mbalestrini/mpw6_caravel_hacks_soc_bringup/devlog/mpw6_048-Caravel_serial_test.png

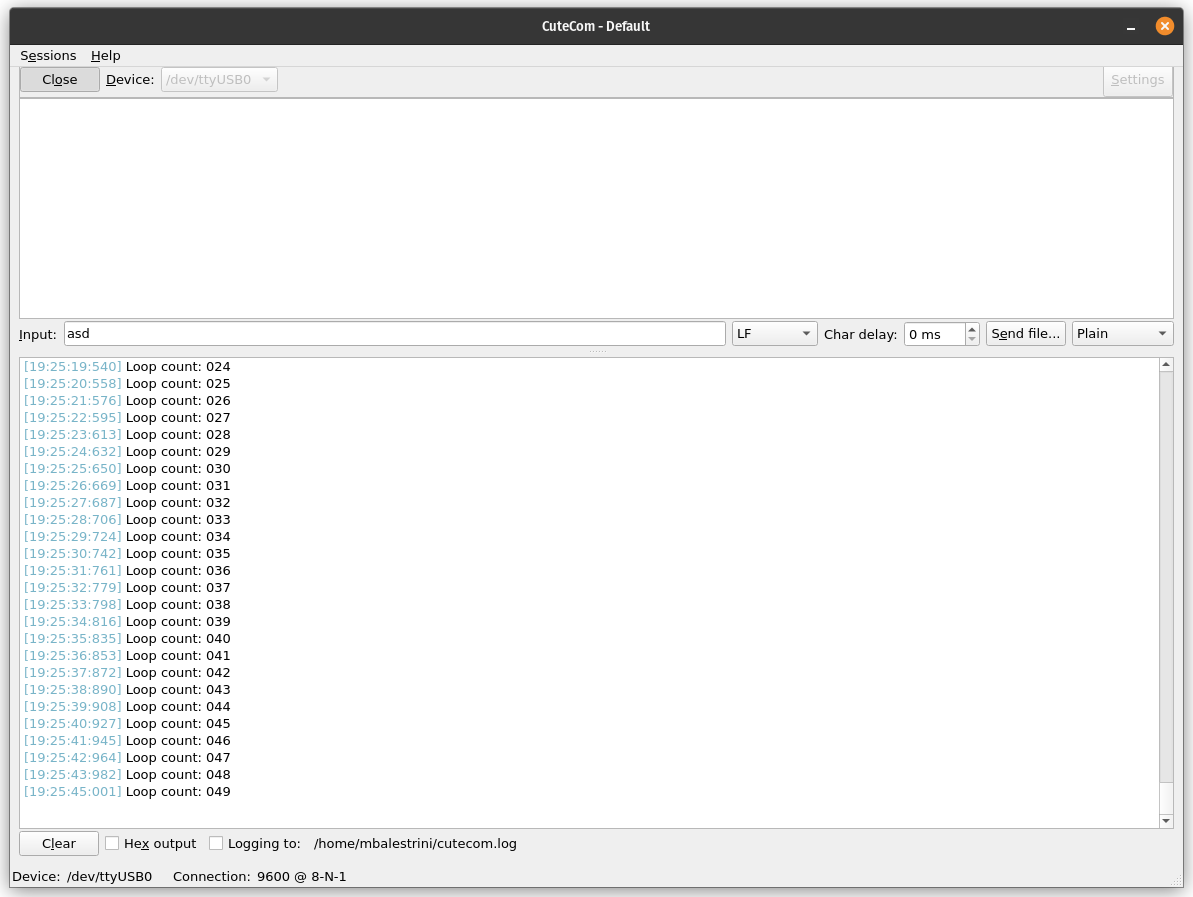
devlog/mpw6_048-Caravel_serial_test.png
