mbalestrini/mpw6_caravel_hacks_soc_bringup/devlog/mpw6_048-first_test-Clock_X1.png

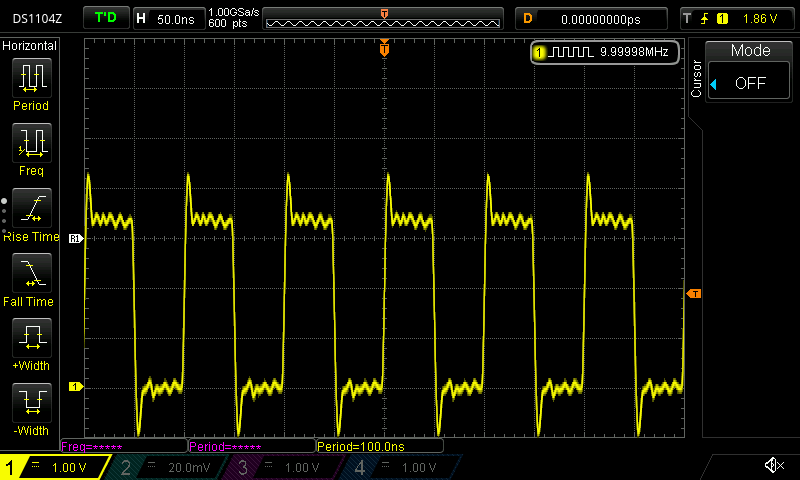
devlog/mpw6_048-first_test-Clock_X1.png
