mbalestrini/mpw6_caravel_hacks_soc_bringup/devlog/mpw6_048-first_test-Init_Sequence-Screenshot from 2023-12-30 17-56-38.png

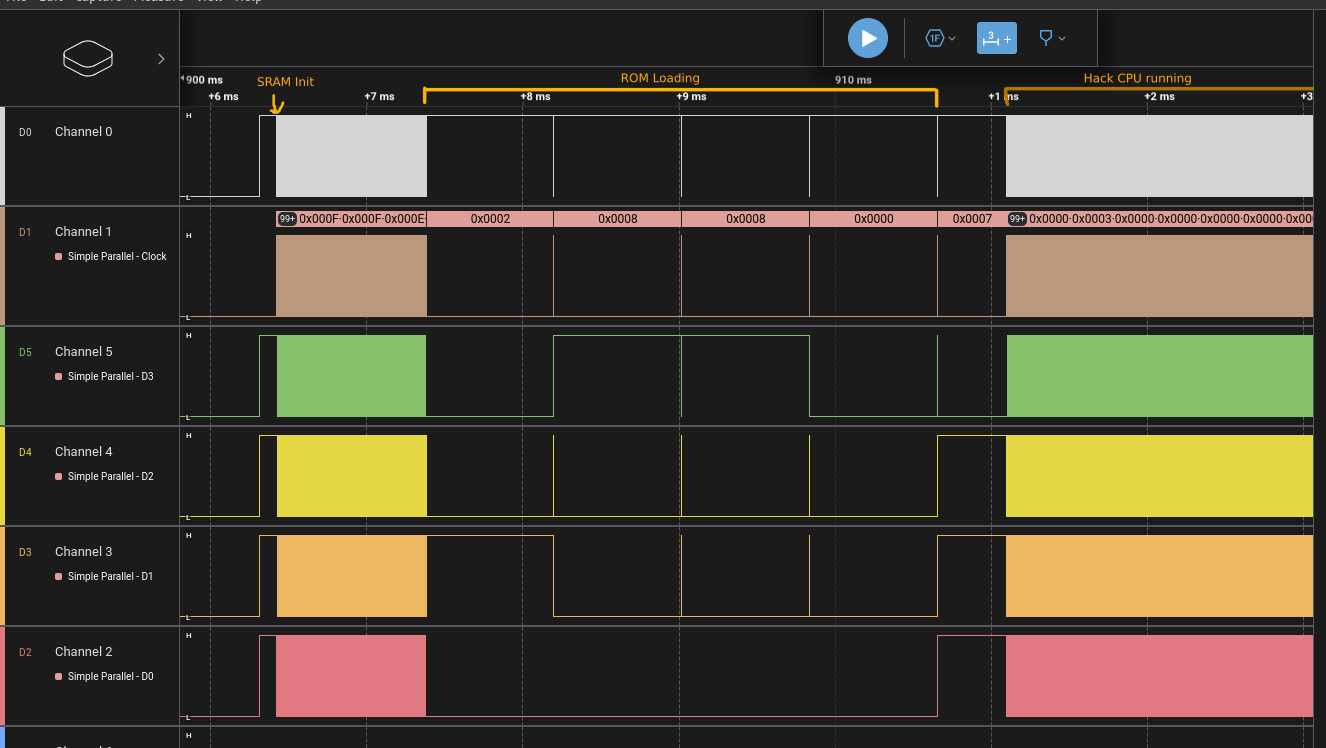
devlog/mpw6_048-first_test-Init_Sequence-Screenshot from 2023-12-30 17-56-38.png
