mbalestrini/mpw6_caravel_hacks_soc_bringup/devlog/mpw6_048-first_test-IO28-20231228-B.png

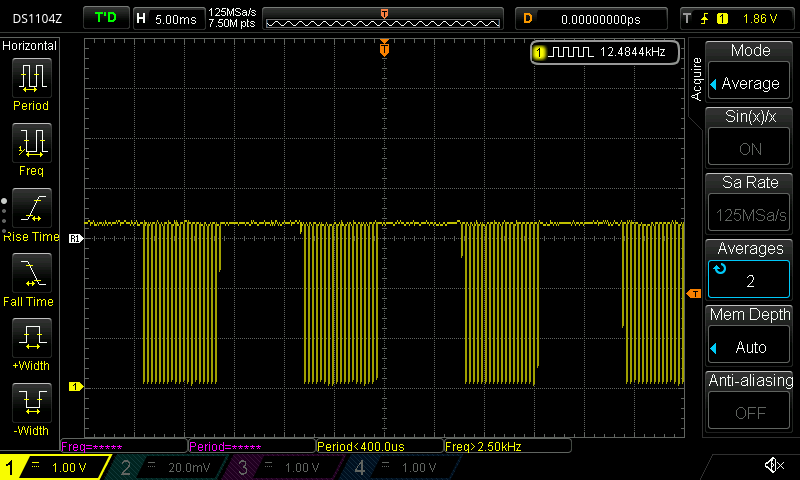
devlog/mpw6_048-first_test-IO28-20231228-B.png
