mbalestrini/mpw6_caravel_hacks_soc_bringup/devlog/mpw6_048-first_test-ROM_Init-Screenshot from 2023-12-30 17-48-50.png

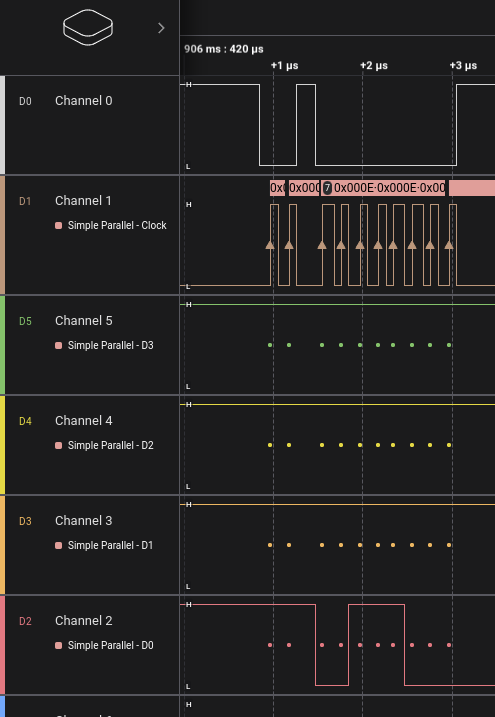
devlog/mpw6_048-first_test-ROM_Init-Screenshot from 2023-12-30 17-48-50.png
