mbalestrini/mpw6_caravel_hacks_soc_bringup/devlog/mpw6_048-test_mem_1-RAM_IO_3_pulldown_10k-RAM_CS_CLK_SIO3-20240123.png

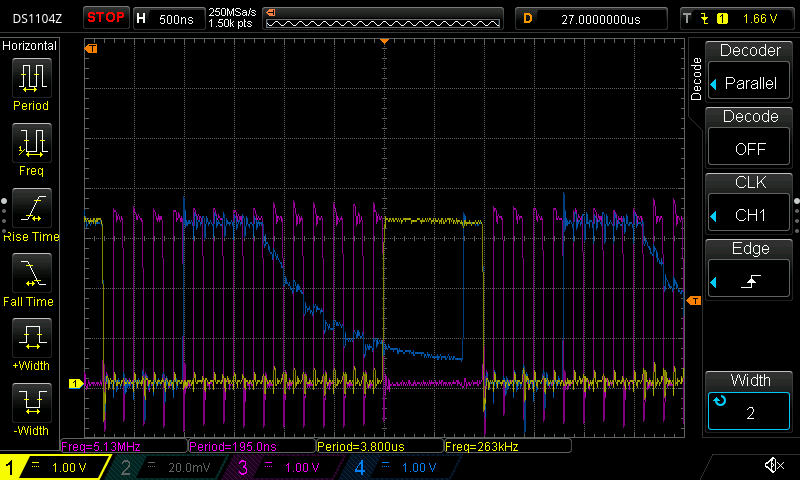
devlog/mpw6_048-test_mem_1-RAM_IO_3_pulldown_10k-RAM_CS_CLK_SIO3-20240123.png
