mbalestrini/mpw6_caravel_hacks_soc_bringup/devlog/_MG_6943.jpg

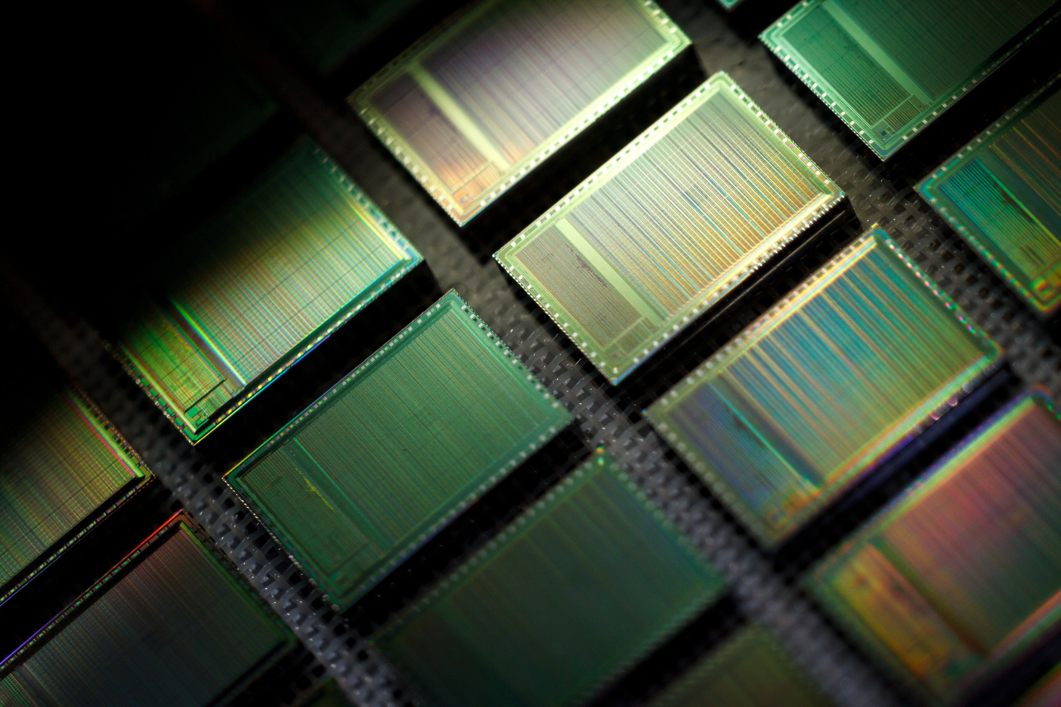
devlog/_MG_6943.jpg
