mbalestrini/mpw6_caravel_hacks_soc_bringup/devlog/_MG_6948.jpg

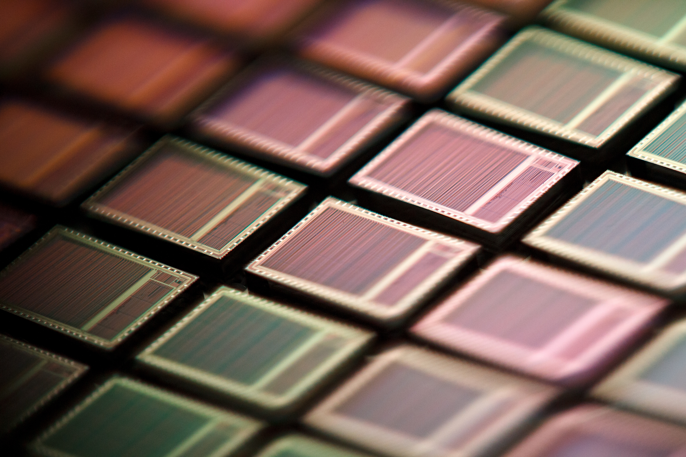
devlog/_MG_6948.jpg
