mbalestrini/mpw6_caravel_hacks_soc_bringup/devlog/DSC09348.jpg

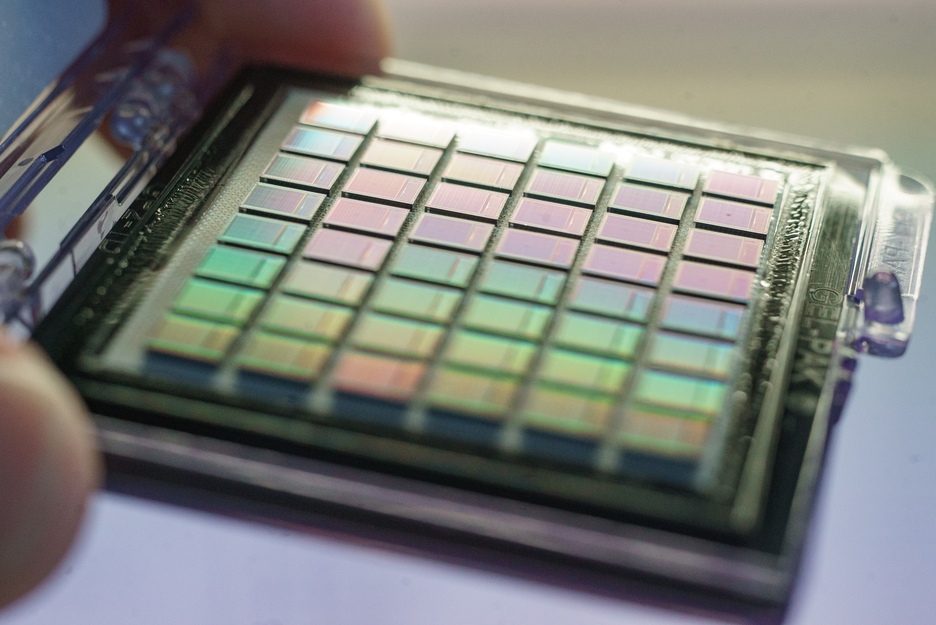
devlog/DSC09348.jpg
