mbalestrini/mpw6_caravel_hacks_soc_bringup/devlog/DSC09561.jpg

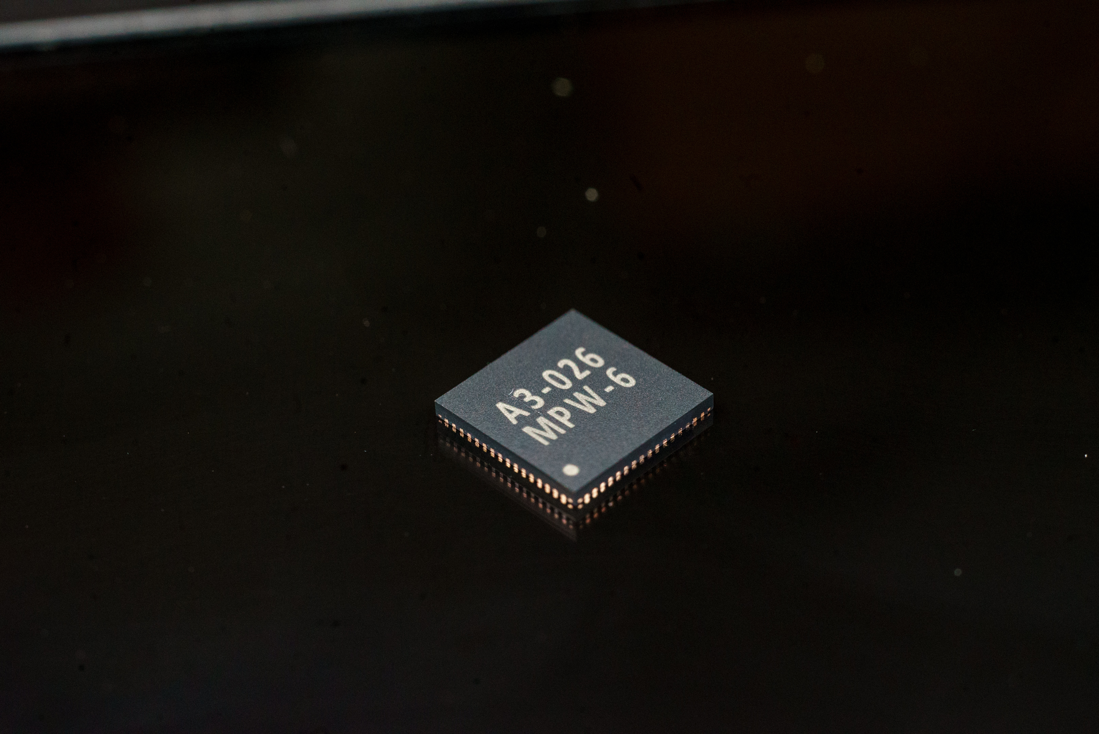
devlog/DSC09561.jpg
