mbalestrini/mpw6_caravel_hacks_soc_bringup/devlog/PXL_20231228_205425441.jpg

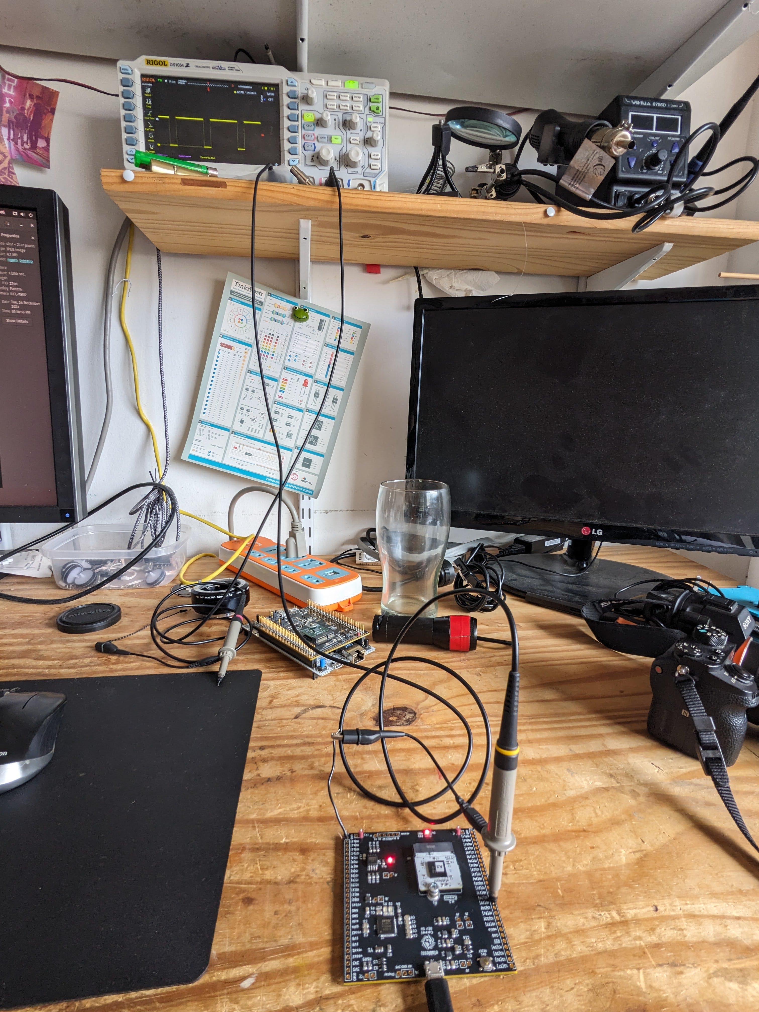
devlog/PXL_20231228_205425441.jpg
