mbalestrini/mpw6_caravel_hacks_soc_bringup/devlog/PXL_20231229_003644289.jpg

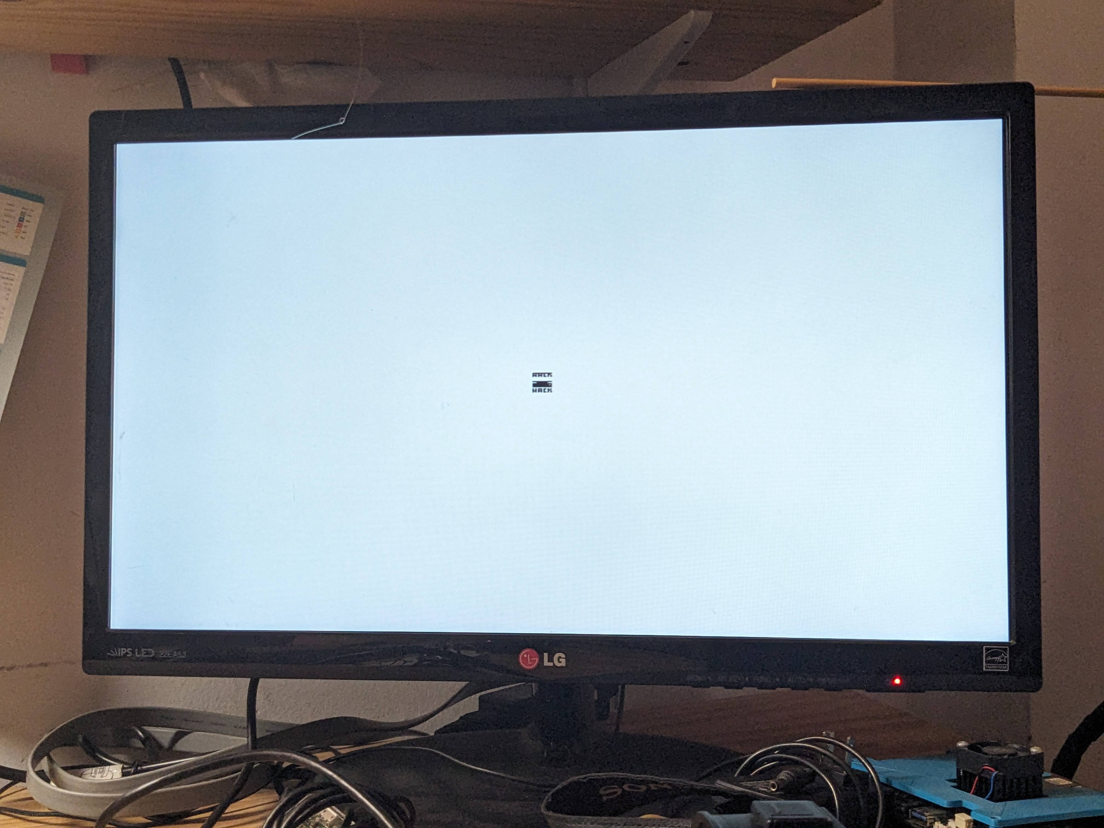
devlog/PXL_20231229_003644289.jpg
