mbalestrini/mpw6_caravel_hacks_soc_bringup/devlog/PXL_20231229_003654547.jpg

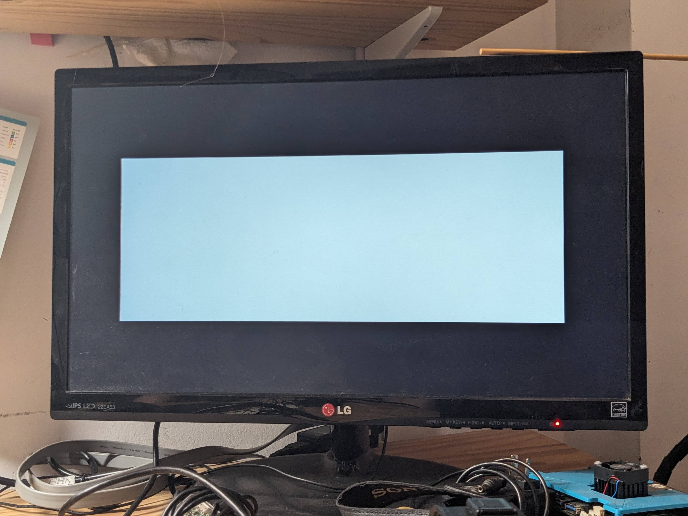
devlog/PXL_20231229_003654547.jpg
