mbalestrini/mpw6_caravel_hacks_soc_bringup/devlog/PXL_20231229_004134263.jpg

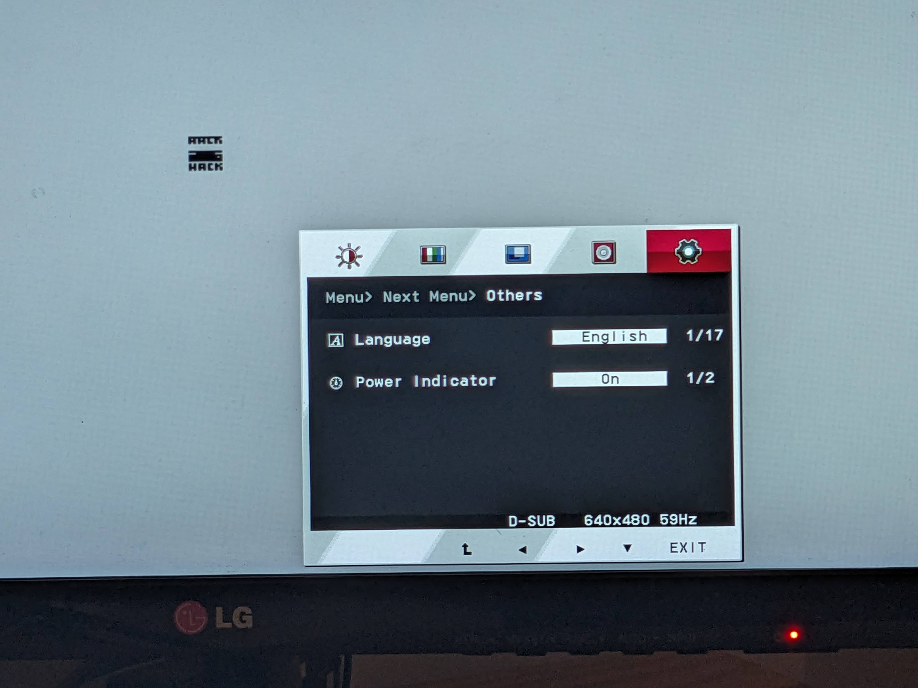
devlog/PXL_20231229_004134263.jpg
