mbalestrini/mpw6_caravel_hacks_soc_bringup/devlog/PXL_20231230_204112461.jpg

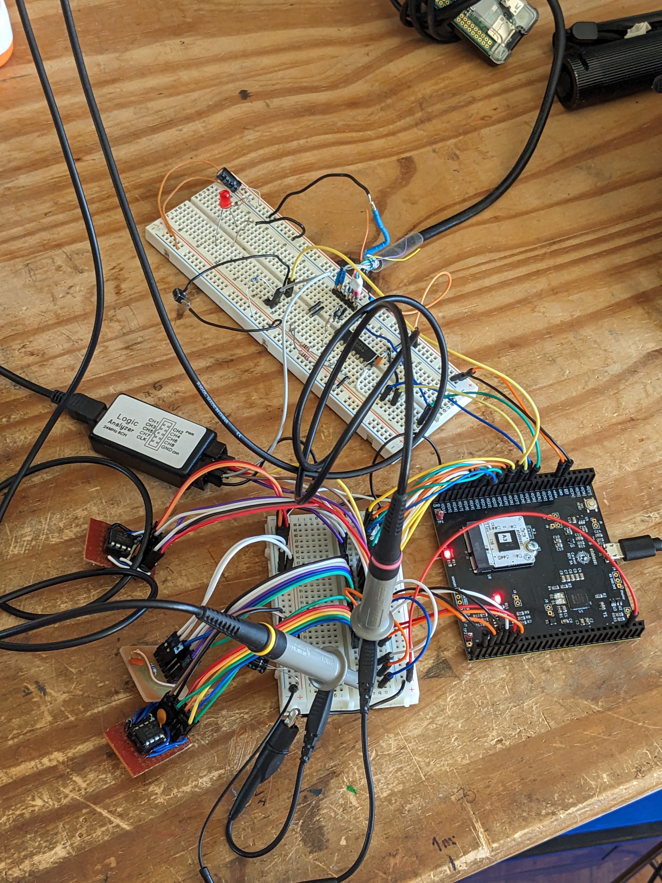
devlog/PXL_20231230_204112461.jpg
