mbalestrini/mpw6_caravel_hacks_soc_bringup/devlog/PXL_20231230_231902643.jpg

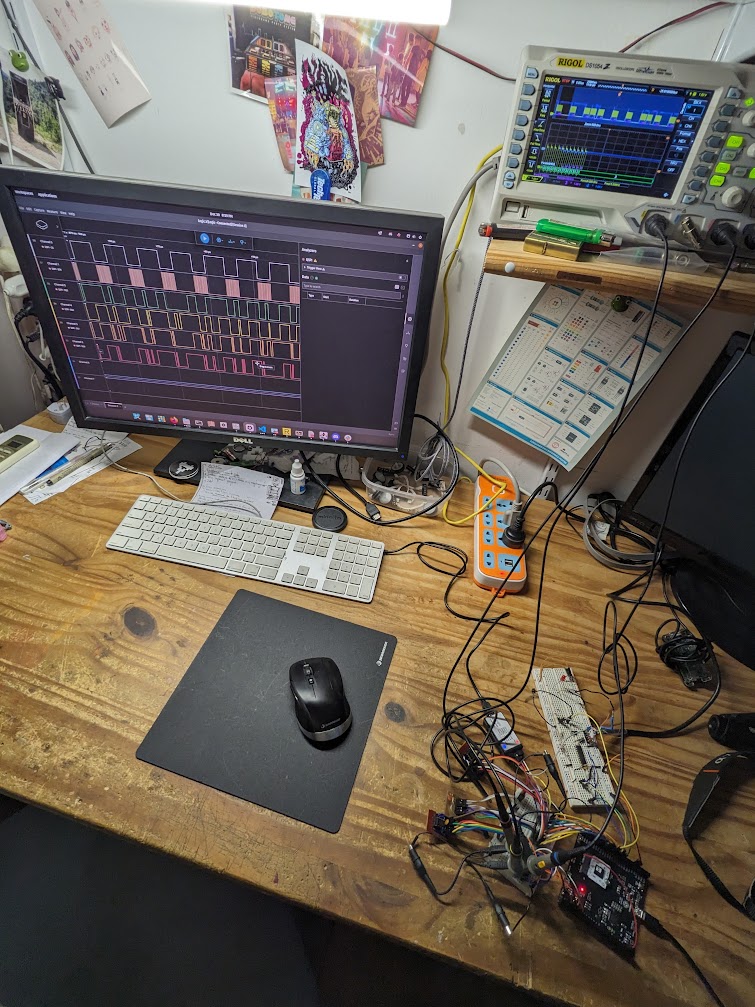
devlog/PXL_20231230_231902643.jpg
